zeugmaster/nucula-board/docs/oled24/top-contact-layout.png

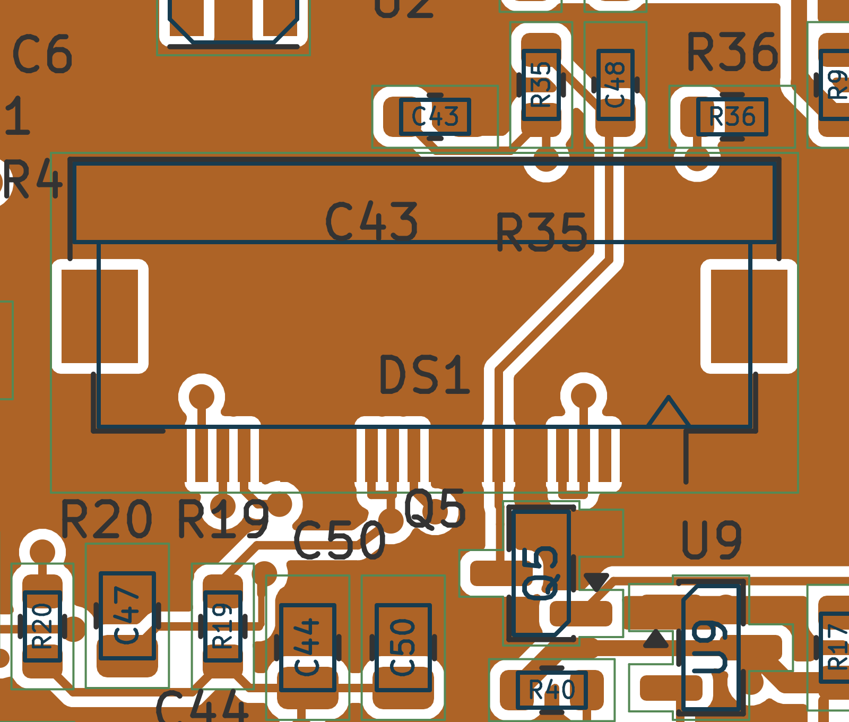
docs/oled24/top-contact-layout.png
