zeugmaster/nucula-board/docs/pcb/copper-layers.png

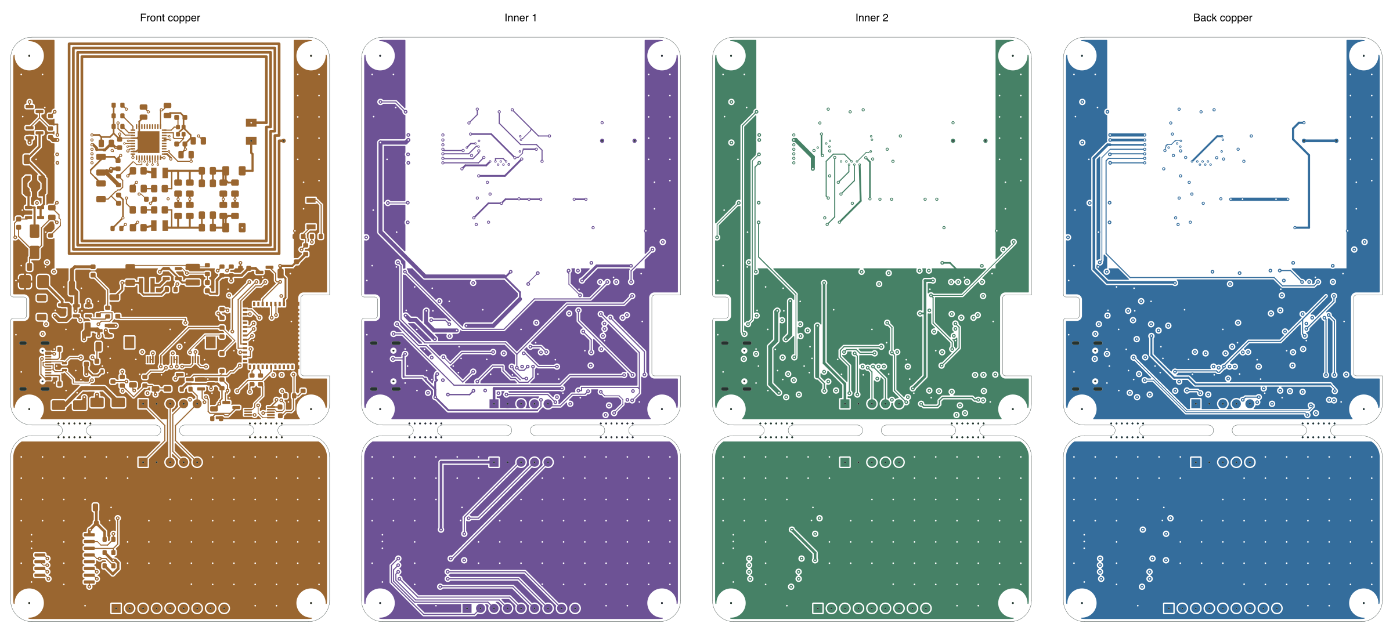
docs/pcb/copper-layers.png
