zeugmaster/nucula-board/docs/pcb/nfc.png

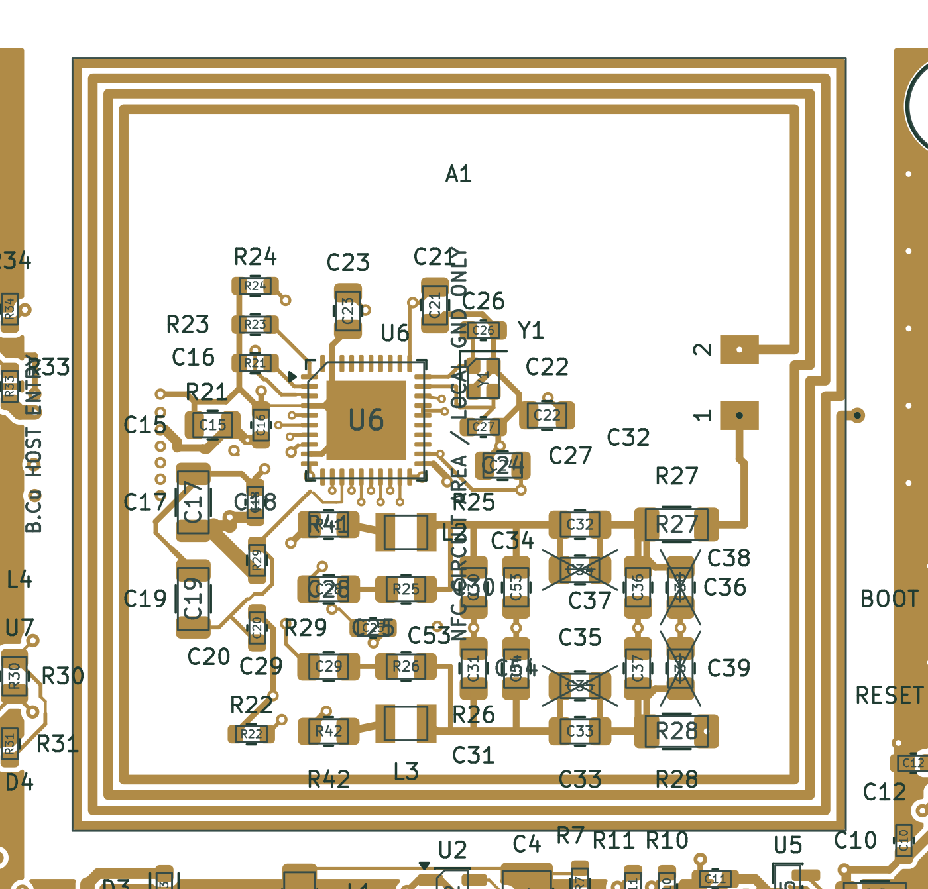
docs/pcb/nfc.png
