zeugmaster/nucula-board/parts documentation/i2c-display-breakout-schematic.png.png

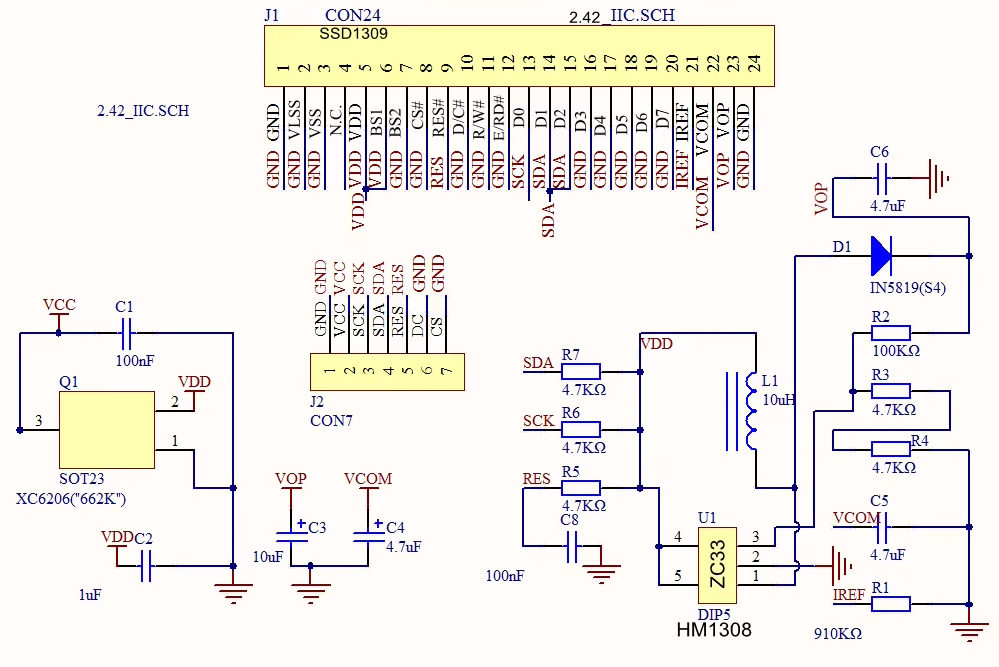
parts documentation/i2c-display-breakout-schematic.png.png
