zeugmaster/nucula-board/parts documentation/FH12A-24S-0.5SH-drawing.pdf

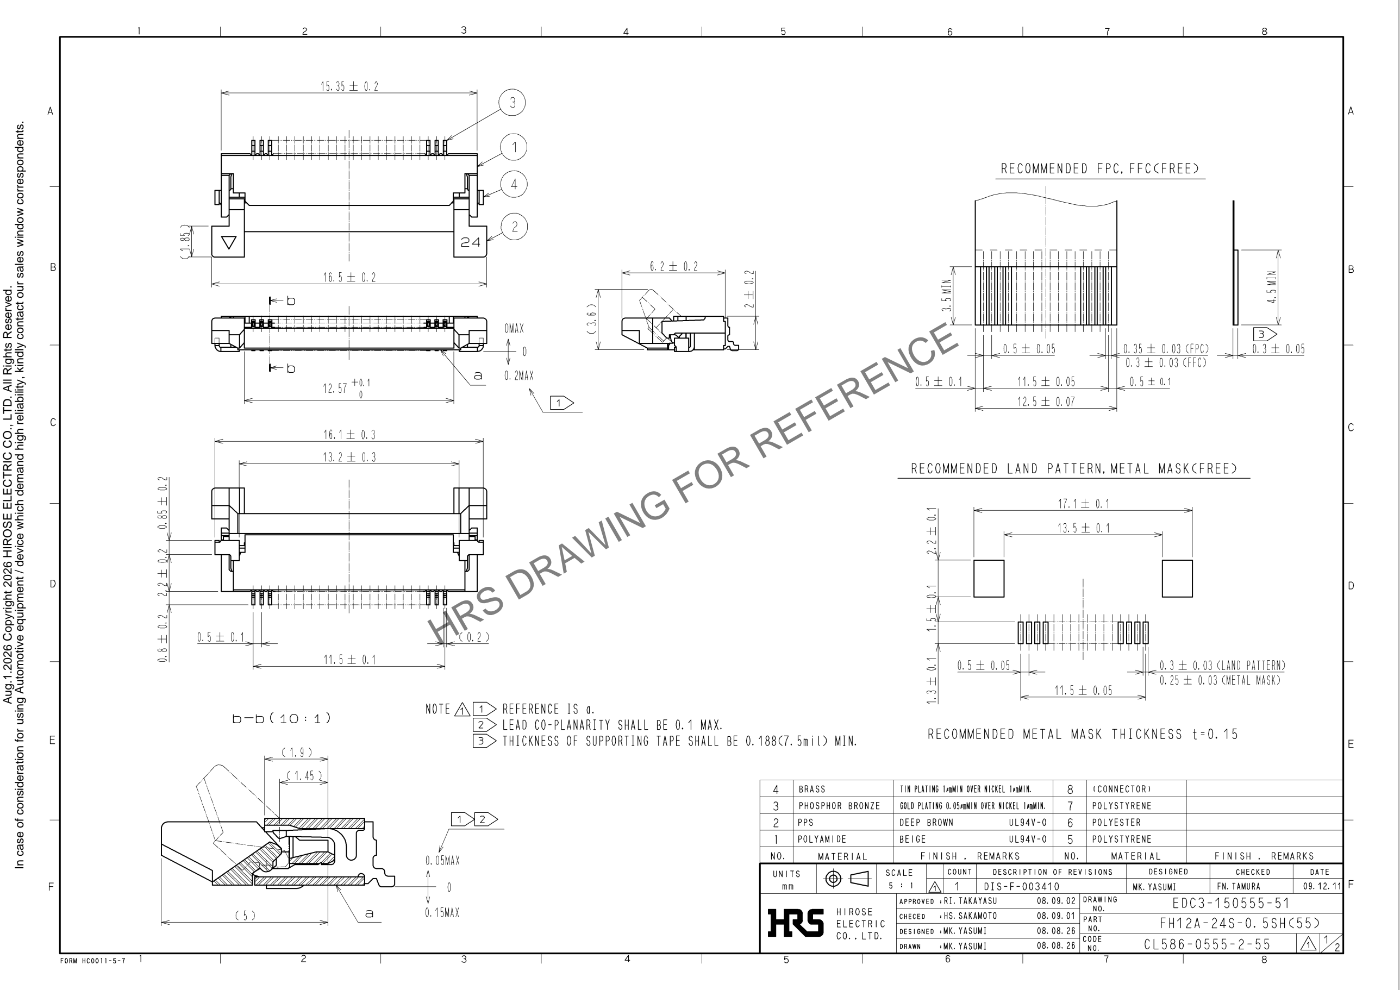
[picture p13: page 1]

HRS DRAWING FOR REFERENCE

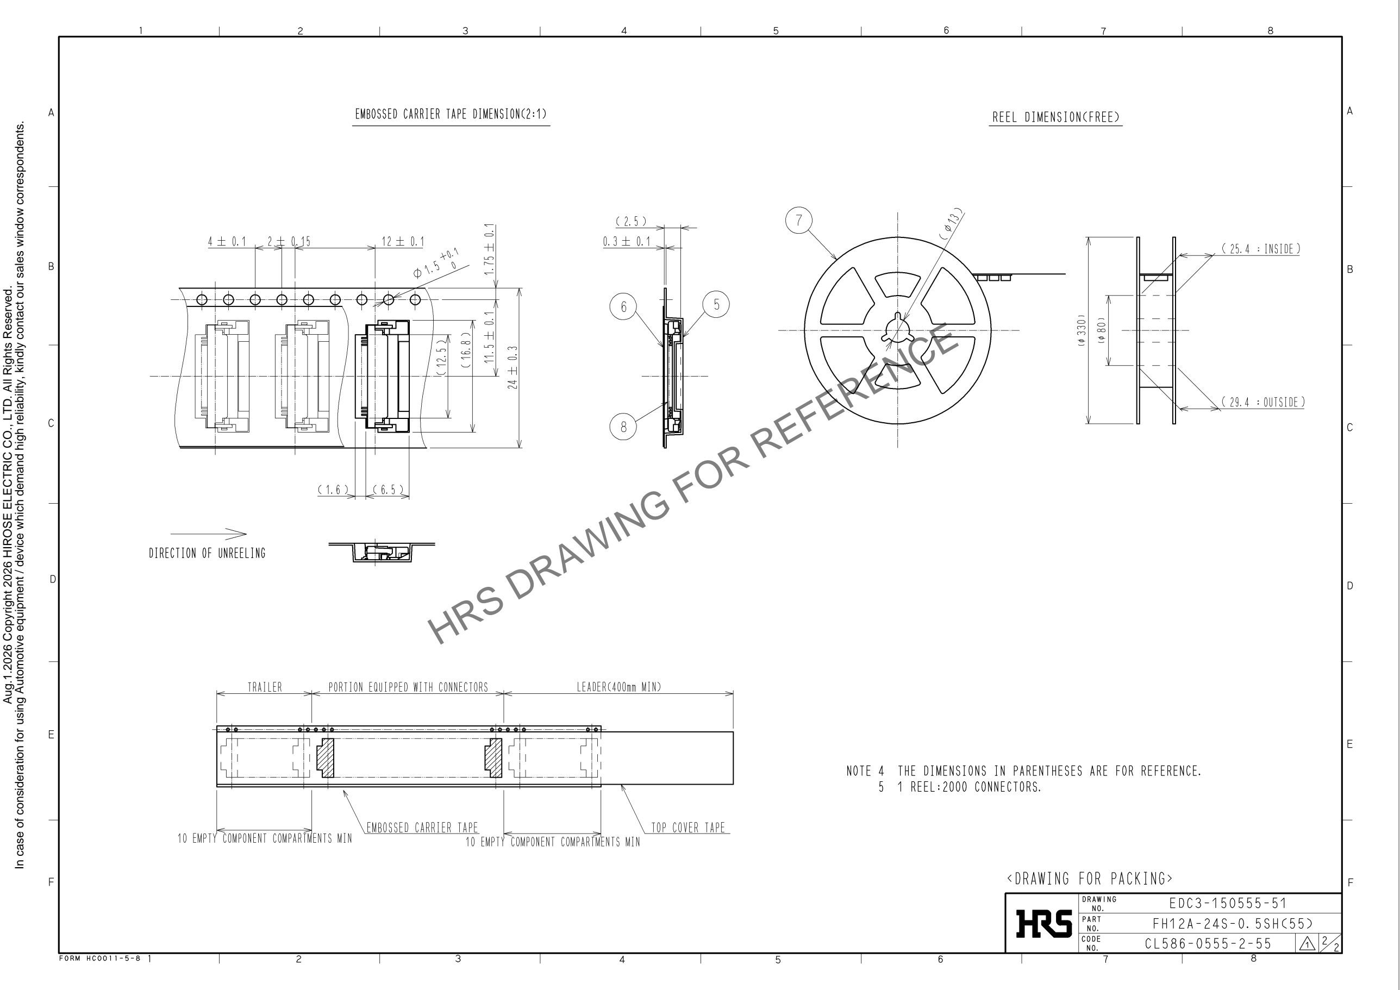
[picture p14: page 2]

HRS DRAWING FOR REFERENCE
