zeugmaster/nucula-board/parts documentation/2.42inch-OLED-Module-Schematic.pdf

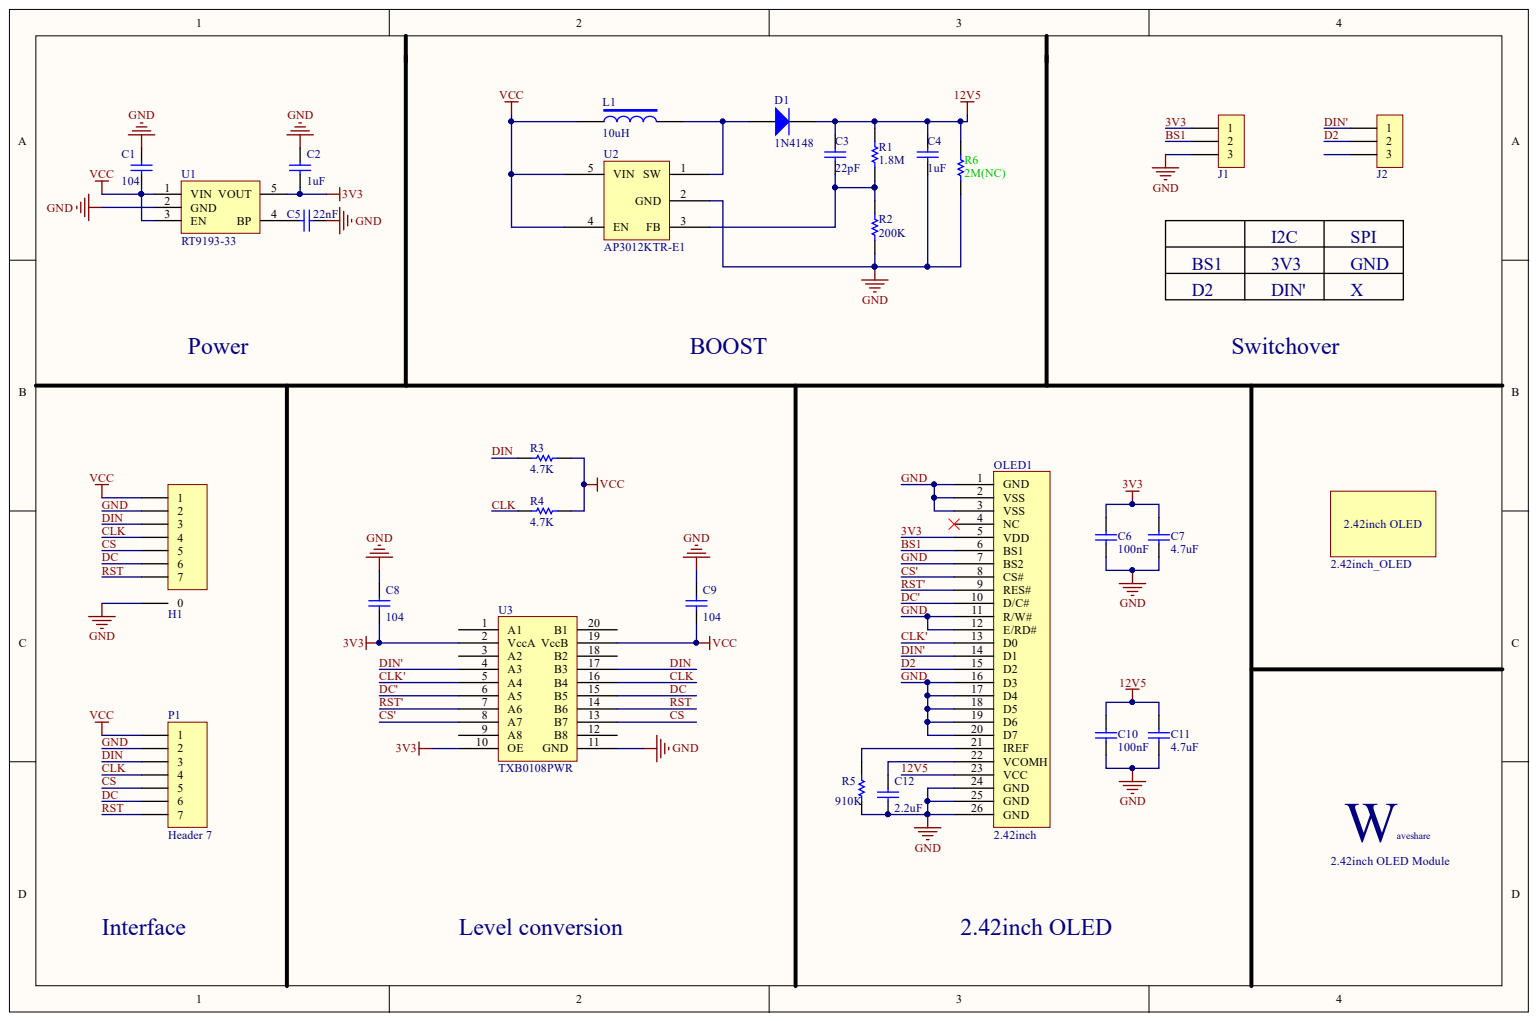
[picture p35: page 1]

GND 2

I2C | SPI

BS1 | 3V3 | GND
D2 | DIN' | X

12V5 | | VCC 23

VCOMH 22

GND 24
GND 25
