zeugmaster/nucula-board/manufacturing/production-2026-10-09/drawings/fabrication-outline.pdf

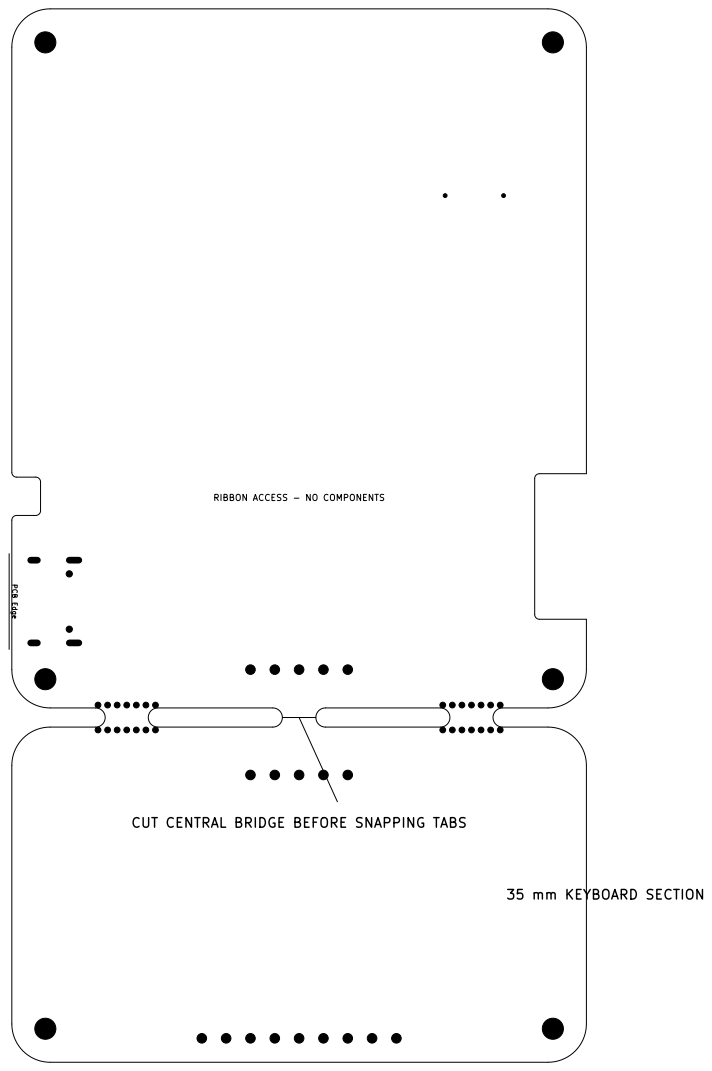
[picture p36: page 1]

RIBBON ACCESS - NO COMPONENTS CUT CENTRAL BRIDGE BEFORE SNAPPING TABS

35 mm KEYBOARD SECTION PCB Edge
