zeugmaster/nucula-board/manufacturing/production-2026-10-09/validation/rev-A-usb-battery-2026-10-06.pdf

# REV A · USB BACKFEED CHECK

## A VBUS · C14 pad 1

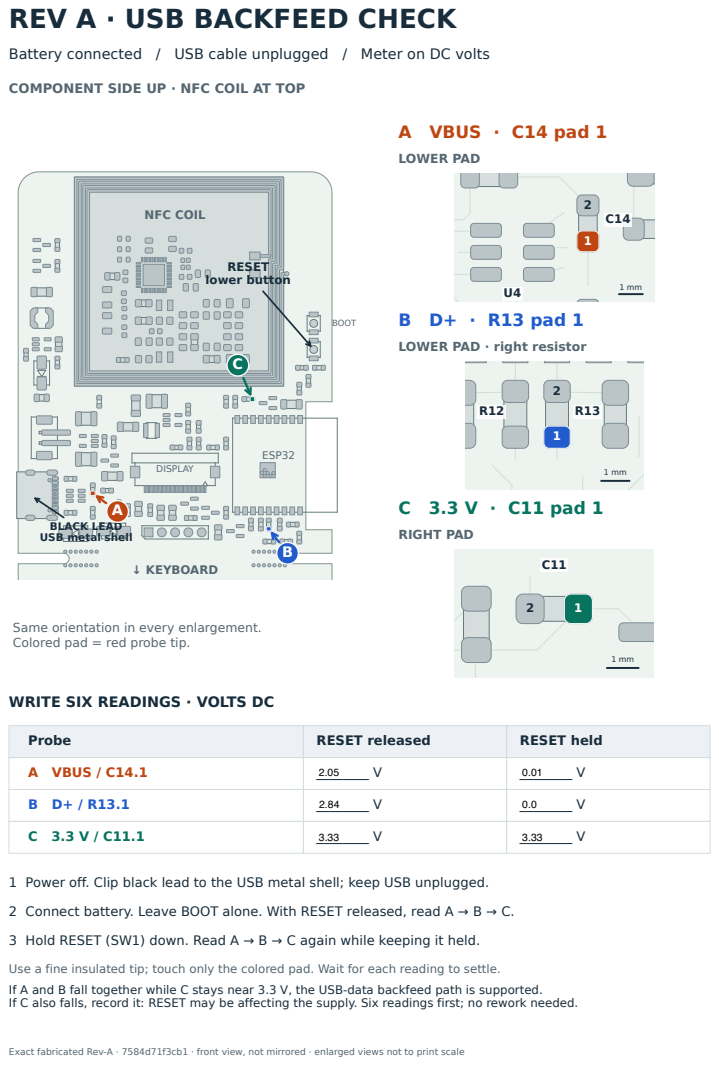
[picture p37: page 1]
NFC COIL; ↓ KEYBOARD; ESP32; DISPLAY; BOOT; RESET lower button; Probe; RESET released; RESET held; A VBUS / C14.1; Battery connected /; USB cable unplugged / Meter on DC volts; LOWER PAD; · R13 pad 1; C11 pad 1; RIGHT PAD

COMPONENT SIDE UP · NFC COIL AT TOP

LOWER PAD · right resistor

BLACK LEAD
USB metal shell

Same orientation in every enlargement.
Colored pad = red probe tip.

WRITE SIX READINGS · VOLTS DC

1 Power off. Clip black lead to the USB metal shell; keep USB unplugged.

2 Connect battery. Leave BOOT alone. With RESET released, read A → B → C.

3 Hold RESET (SW1) down. Read A → B → C again while keeping it held.

Use a fine insulated tip; touch only the colored pad. Wait for each reading to settle.
If A and B fall together while C stays near 3.3 V, the USB-data backfeed path is supported.
If C also falls, record it: RESET may be affecting the supply. Six readings first; no rework needed.

Exact fabricated Rev-A · 7584d71f3cb1 · front view, not mirrored · enlarged views not to print scale
