zeugmaster/nucula-board/parts documentation/PN7160_schematic-3.pdf

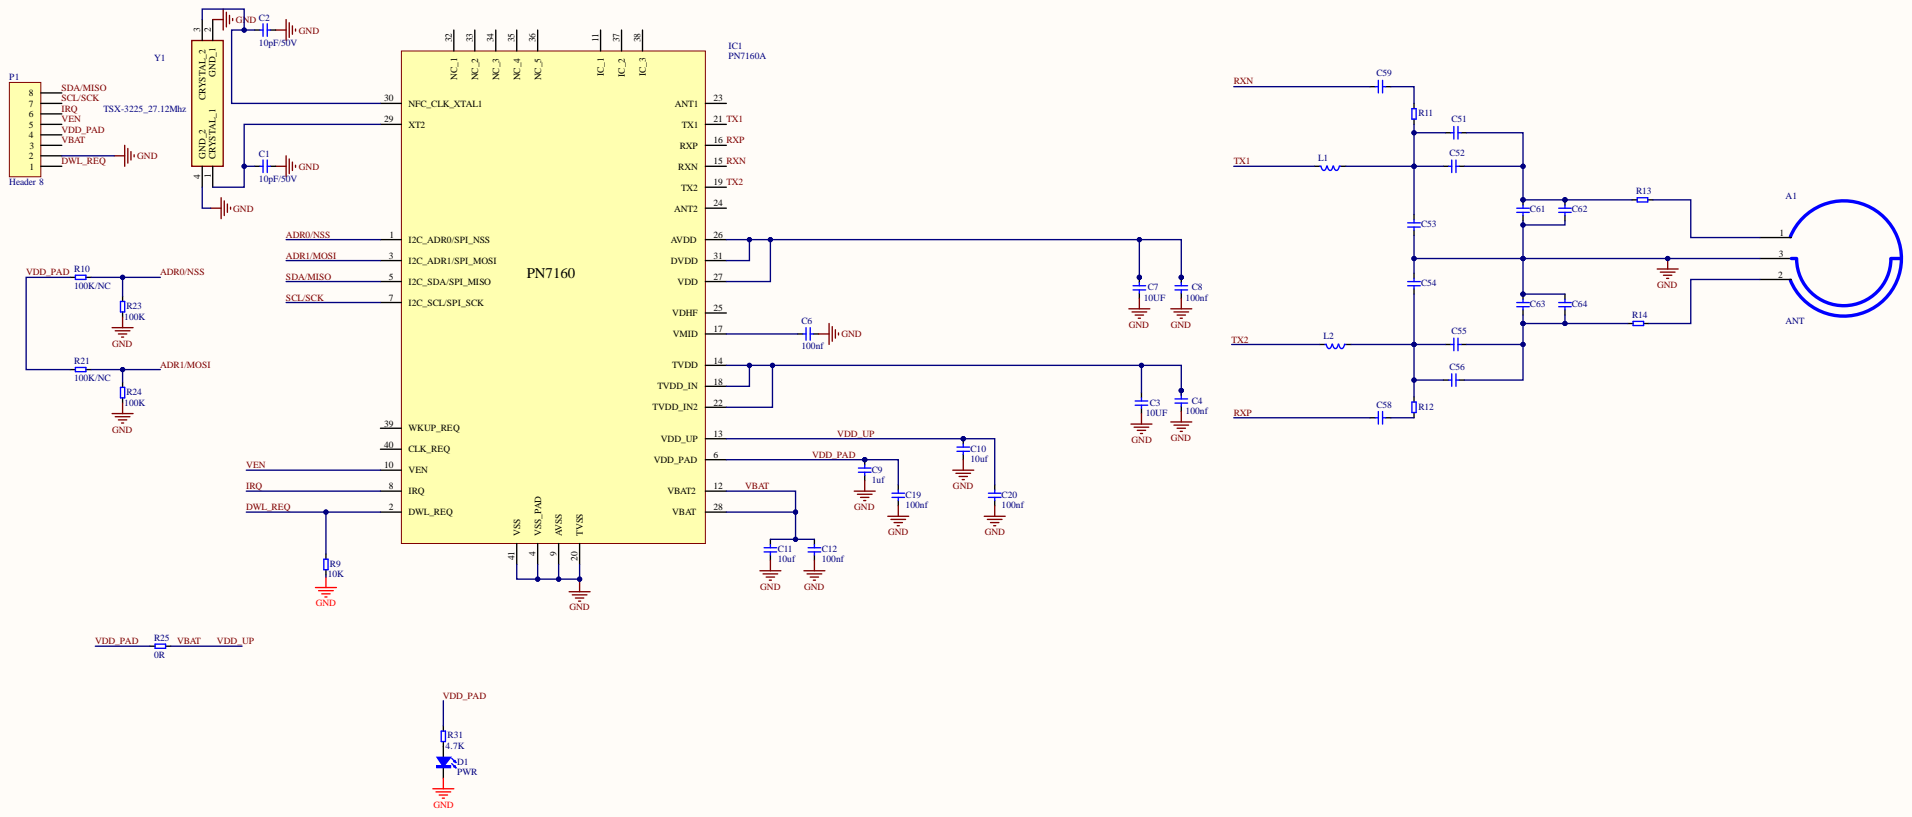
[picture p38: page 1]

C9 VBAT 1uf
