zeugmaster/nucula-board/manufacturing/production-2026-10-09/drawings/assembly-top.pdf

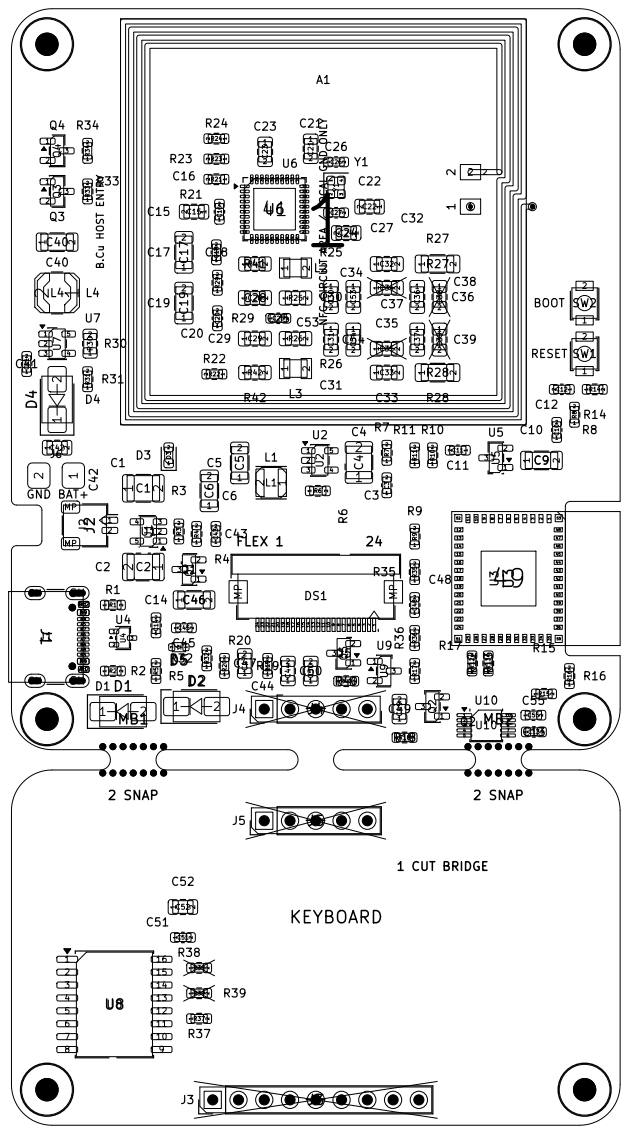
[picture p39: page 1]
