zeugmaster/nucula-board/manufacturing/production-2026-10-09/drawings/layers.pdf

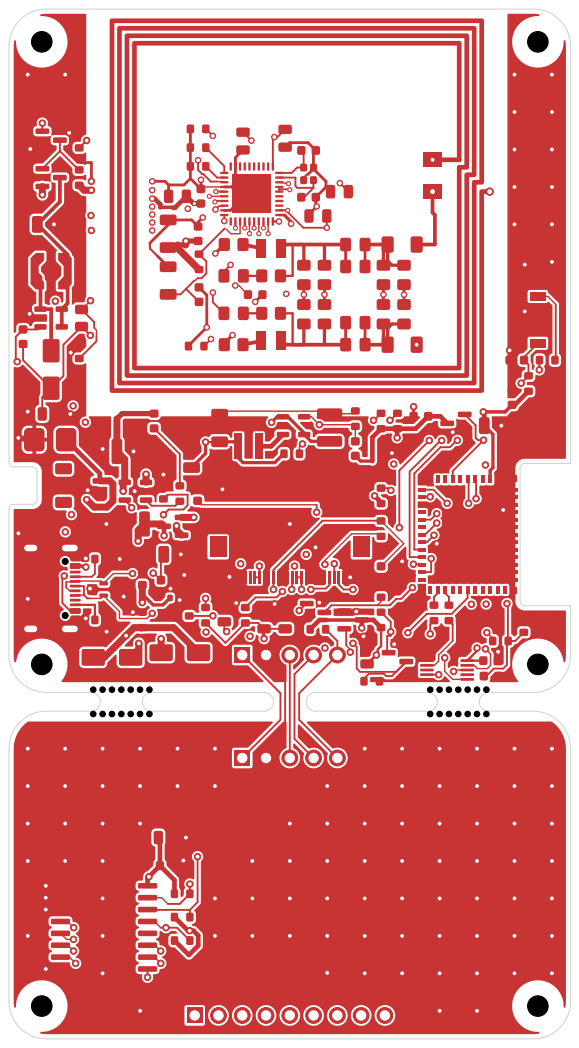
[picture p40: page 1]

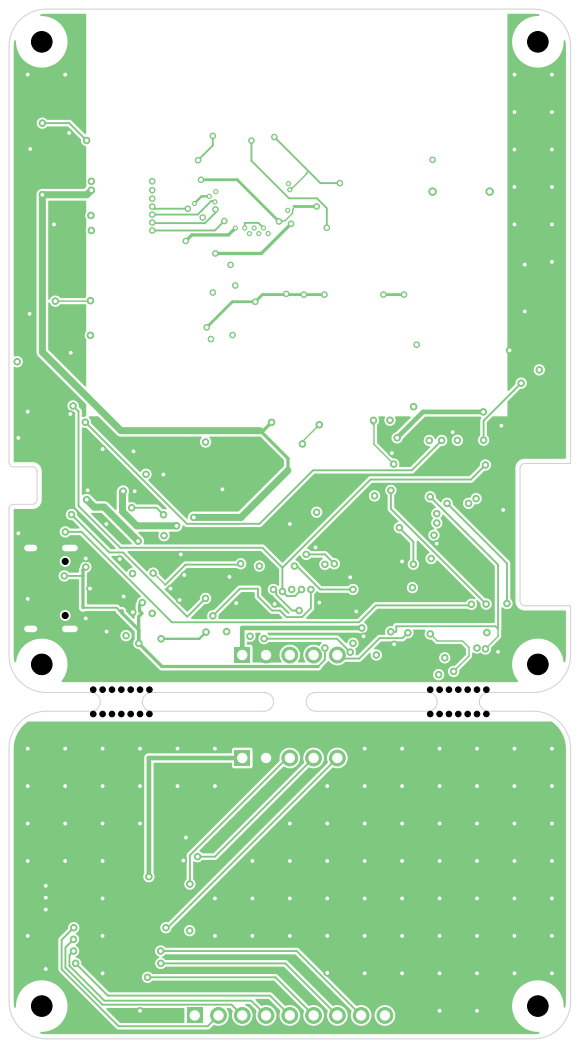
[picture p41: page 2]

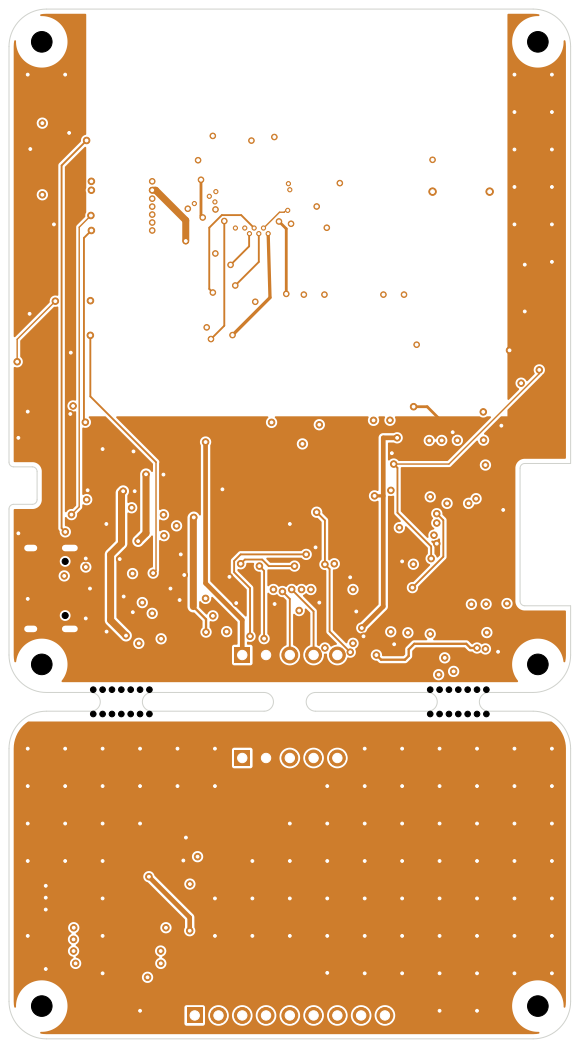
[picture p42: page 3]

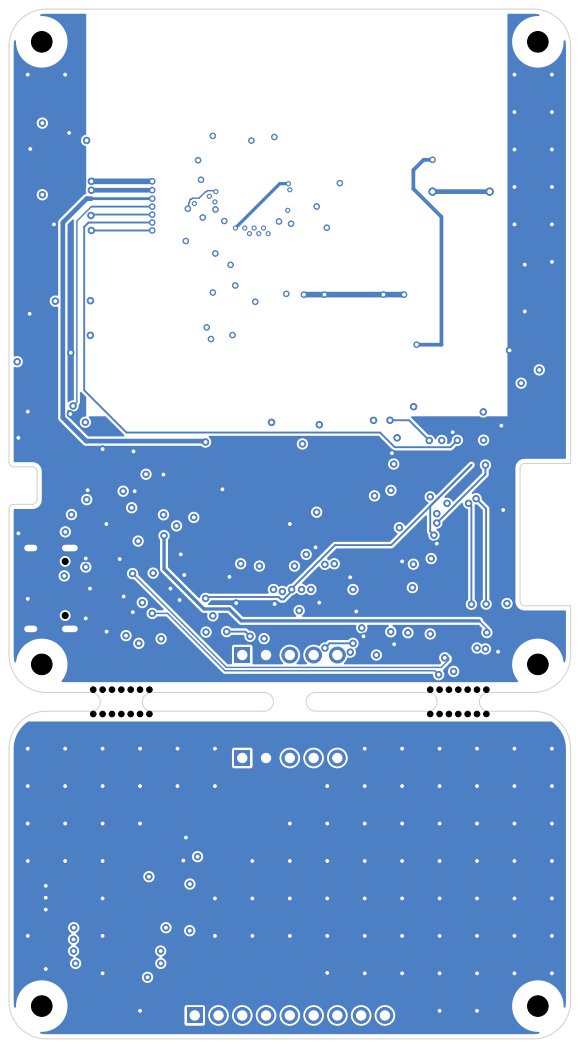
[picture p43: page 4]

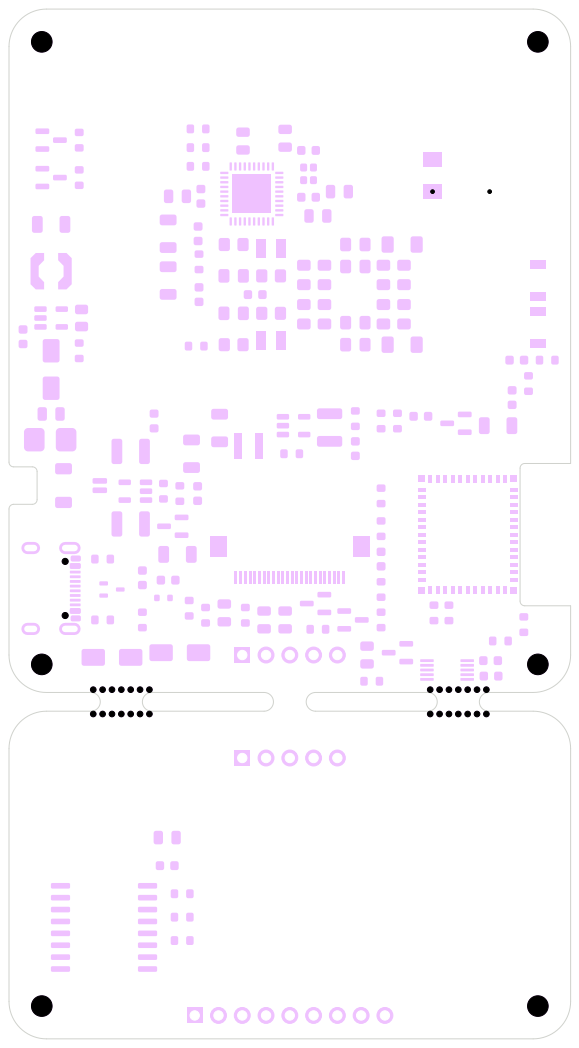
[picture p44: page 5]

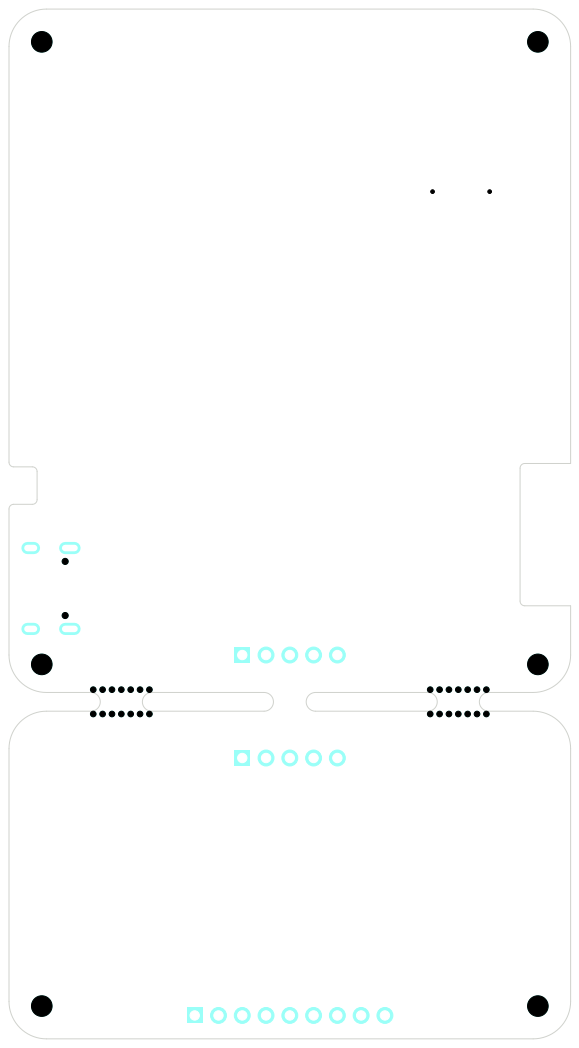
[picture p45: page 6]

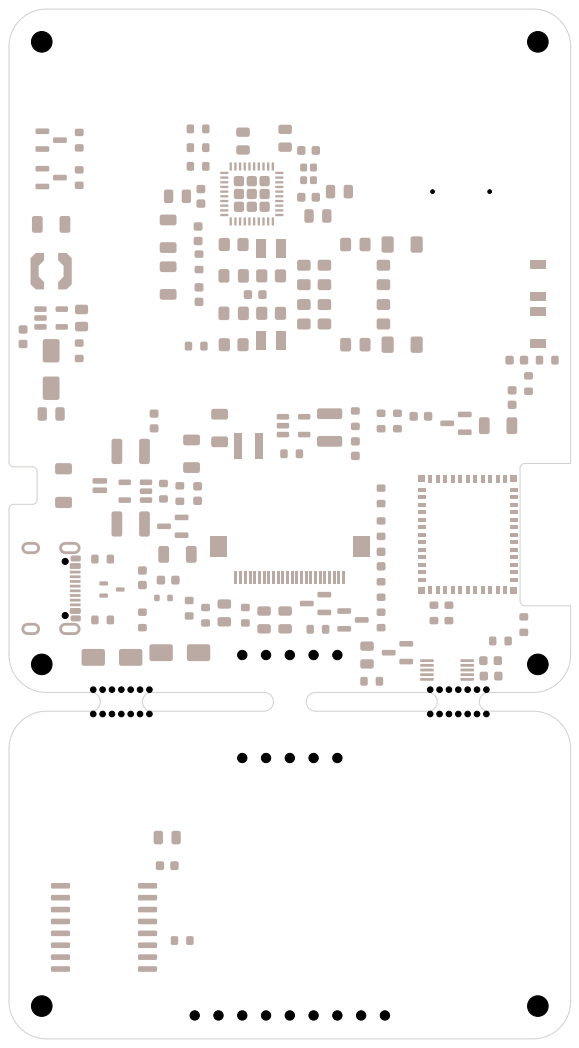
[picture p46: page 7]
