zeugmaster/nucula-board/manufacturing/production-2026-10-09/drawings/placement-reference.pdf

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

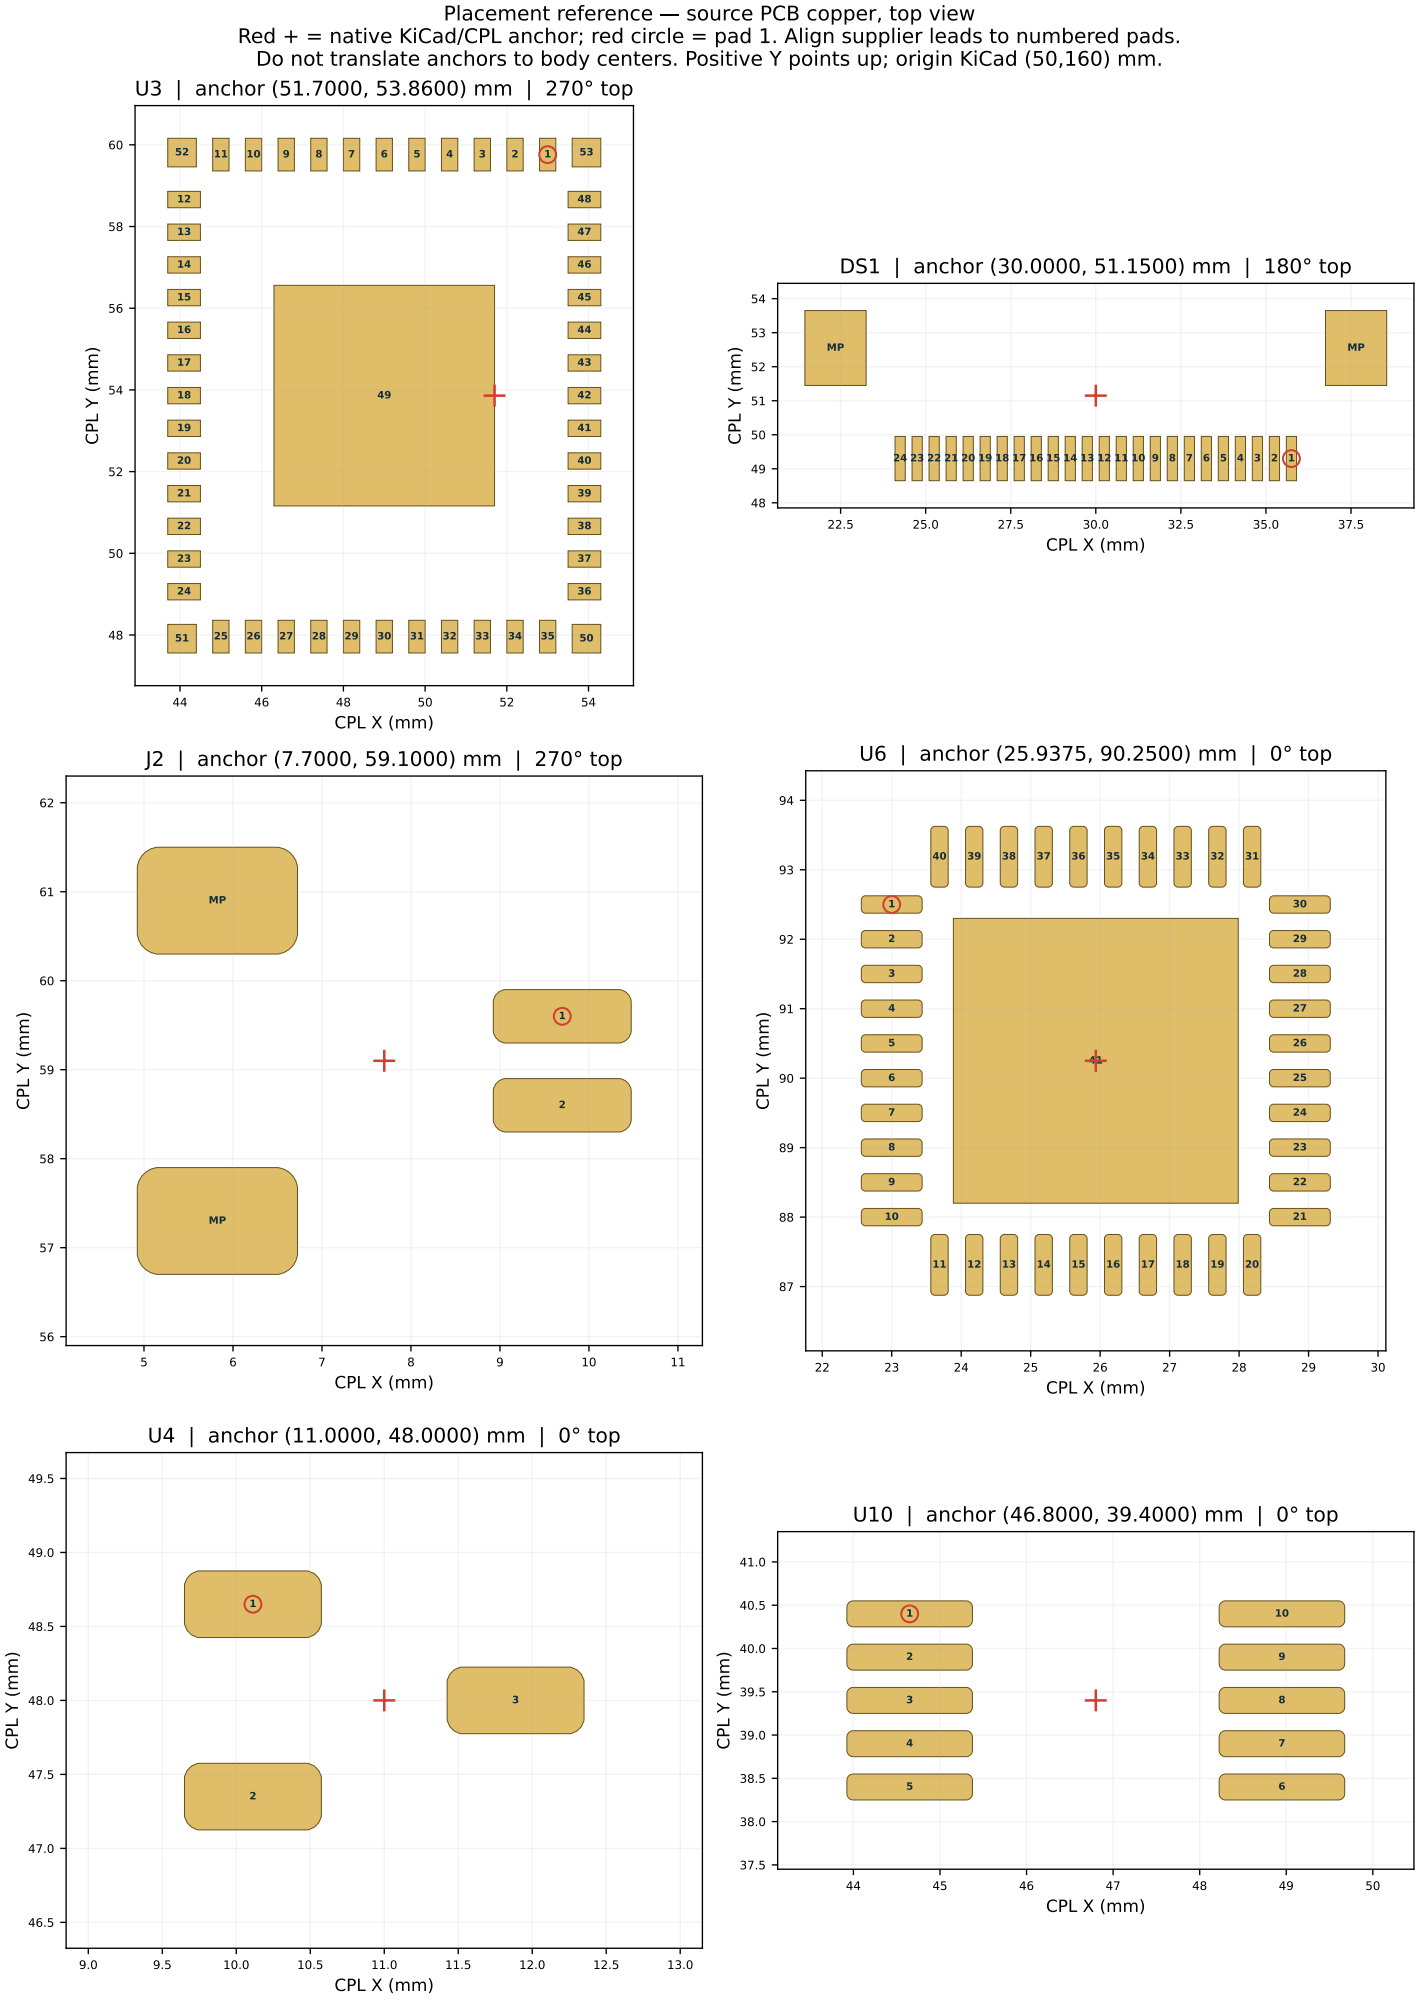
[picture p47: page 1]
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
