zeugmaster/nucula-board/manufacturing/production-2026-10-09/validation/nfc/matching.cir

Nucula NFC full differential passive model / 13.56MHz
* Assumed bare-coil model; no nonlinear PN7160 or tag coupling.
* Coilcraft 0805CS-151XGLC; Rvar frozen at f0.
VP txp 0 DC 0 AC 0.5 0
VN txn 0 DC 0 AC 0.5 180
.subckt emc a b
Rd a x 0.56
Rskin x y 0.82117308772268
Lcore y b 1.49e-07
Cpar x z 1.1e-13
Rpar z b 24.0
.ends emc
XLP txp ep emc
XLN txn en emc
Rcp0 ep ep0 .03
Cp0 ep0 0 330p
Rcn0 en en0 .03
Cn0 en0 0 330p
Rcpt ep ept .03
Cpt ept 0 33p
Rcnt en ent .03
Cnt ent 0 33p
Rcp1 ep sp .03
Cp1 sp mp 68p
Rcn1 en sn .03
Cn1 sn mn 68p
Rcp2 mp mp0 .03
Cp2 mp0 0 100p
Rcn2 mn mn0 .03
Cn2 mn0 0 100p
Rqp mp ap 2.7
Rqn mn an 2.7
Ra ap ai 1.5
La ai an 1.55900493254921e-06
Ca ap an 2e-12
Rrxp ep rp 2200
Rcxp rp rp1 .03
Crxp rp1 rxp 1n
Rinp rxp 0 2200
Rrxn en rn 2200
Rcxn rn rn1 .03
Crxn rn1 rxn 1n
Rinn rxn 0 2200
.ac lin 1 13.56Meg 13.56Meg
.end
